shulltronics/cv-binary-seq-eurorack/outputs/3d_render_exports/cv_sequencer_1.png

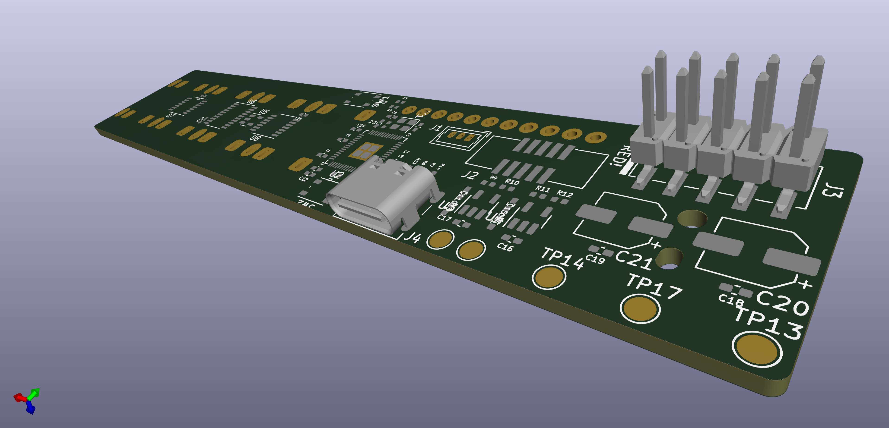
outputs/3d_render_exports/cv_sequencer_1.png
